elferink/iot-shield/software/arduino/iota-mqtt/apa.ino

#include <FastLED.h>

#define LED_PIN     5
#define NUM_LEDS    2
#define BRIGHTNESS  32
#define LED_TYPE    APA102
#define COLOR_ORDER BGR

CRGB leds[NUM_LEDS];

#define APADATAPIN 13 // D7
#define APACLOCKPIN 14 // D5

void setRgbLed(int ledno, CHSV color);

void setupApa() {
  FastLED.addLeds<LED_TYPE, APADATAPIN, APACLOCKPIN, COLOR_ORDER>(leds, NUM_LEDS).setCorrection(TypicalLEDStrip);
  FastLED.setBrightness(BRIGHTNESS);
  apaOff();
}

void apaOff() {
  leds[0] = CRGB::Black;
  leds[1] = CRGB::Black;
  FastLED.show();
}

void setRgbLed(int ledno, CHSV color) {
  leds[ledno].setHSV(color.hue, color.sat, color.val);
  FastLED.show();
}
