elferink/iot-shield/software/arduino/iota-mqtt/temperature.ino

#include <Wire.h>
#include <LM75.h>

LM75 sensor;

int temperature_lastUpdate = 0;
int temperature_update_interval = 60000; // 1 minute

float lastTemperature = 0;

void setupTemperature() {
  Wire.begin();
  updateTemperature();
}

void updateTemperature() {
  sensor.shutdown(false);
  delay(100);
  lastTemperature = sensor.temp();
  
  Serial.print(lastTemperature);
  Serial.println(" C");

  pubFloat("temperature", lastTemperature);
  
  sensor.shutdown(true);
}

void loopTemperature() {
  if (millis() > temperature_update_interval && 
      (millis() - temperature_update_interval) > temperature_lastUpdate) {
    updateTemperature();
    temperature_lastUpdate = millis();
  }
}
